glidingthroughspace/paper-tracker/paper/template/00_Latex/kopfundFusszeile.tex

%% spellcheck-off
% ---- Metainformation für das PDF Dokument
\hypersetup{
	pdftitle    = {\thetitle},
	pdfsubject  = {\arbeit},
	pdfauthor   = {\theauthor},
	%pdfkeywords = {Keywords angeben},
	pdfcreator  = {LaTeX},
	%pdfproducer = {in der Regel pdfTeX}
}

% ---- Definition der Kopf- und Fußzeilen
\clearscrheadfoot                               % Löschen von LaTeX Standard
\automark[section]{chapter}                     % Füllen von section und chapter
%\renewcommand*{\chaptermarkformat}{}            % Entfernt die Kapitelnummer
%\renewcommand*{\sectionmarkformat}{}            % Entfernt die Sectionnummer
% Angaben [für "plain"]{für "scrheadings"}
\ihead[]{}                                      % Kopfzeile links
\chead[]{}                                      % Kopfzeile mitte
\ohead[]{\rightmark}                            % Kopfzeile rechts
\ifoot[]{}                                      % Fußzeile links
\cfoot[]{}                                      % Fußzeile mitte
\ofoot[]{\sffamily\pagemark}                    % Fußzeile rechts
\KOMAoptions{headsepline = 0.1pt, footsepline = 0.1pt}
