glidingthroughspace/paper-tracker/paper/template/01_Standard/sperrvermerk.tex

\chapter*{Sperrvermerk}
Die nachfolgende Arbeit enthält vertrauliche Daten der:
\begin{quote}
	\firmaName \\
	\firmaStrasse \\
	\firmaPlz
\end{quote}

\vspace{0.5cm}

Sie darf als Leistungsnachweis des Studienganges \studiengang{} \studienjahr{} an der DHBW Karlsruhe verwendet und nur zu Prüfungszwecken zugänglich gemacht werden. Über den Inhalt ist Stillschweigen zu bewahren. Veröffentlichungen oder Vervielfältigungen der \arbeit{} - auch auszugsweise - sind ohne ausdrückliche Genehmigung der SAP SE nicht gestattet.

\vspace{0.5cm}

SAP und die SAP Logos sind eingetragene Warenzeichen der SAP SE. Die Wiedergabe von Gebrauchsnamen, Handelsnamen, Warenbezeichnungen usw. in dieser Arbeit berechtigt auch ohne besondere Kennzeichnung nicht zu der Annahme, dass solche Namen im Sinne der Warenzeichen-und Markenschutz-Gesetzgebung als frei zu betrachten wären und daher von jedem benutzt werden dürfen.
