glidingthroughspace/paper-tracker/paper/Studienarbeit.pdf

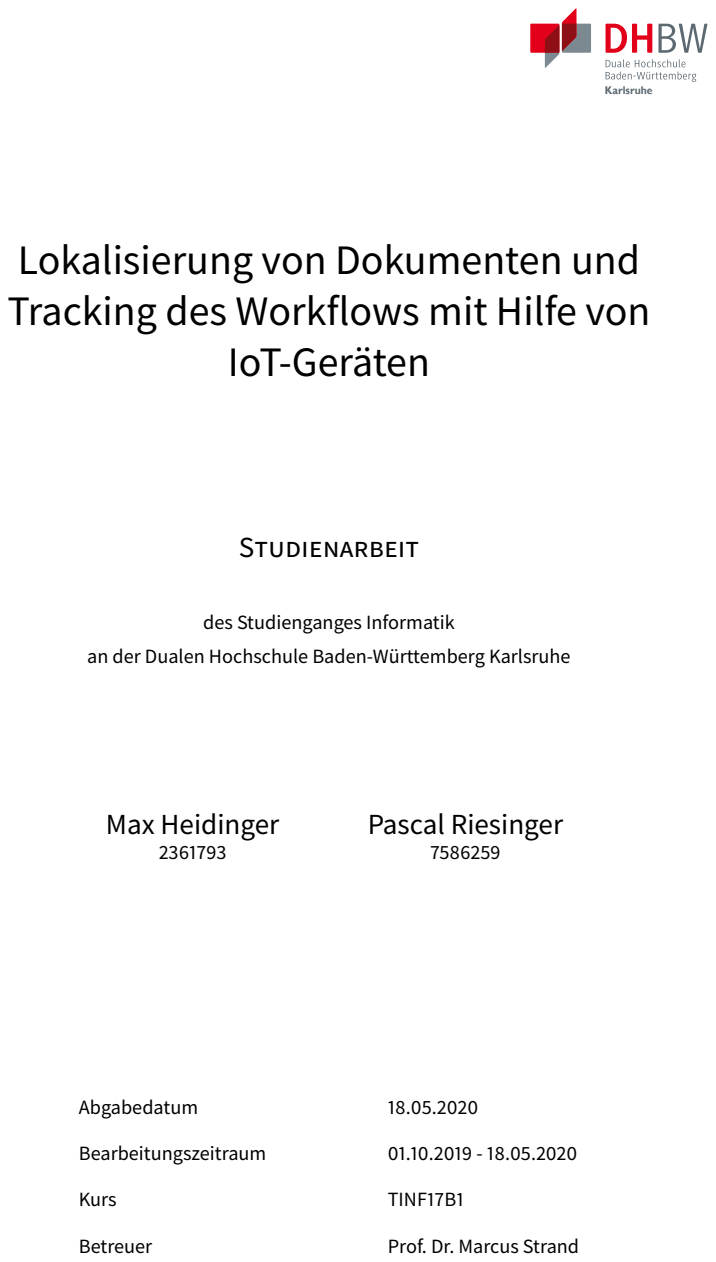
[picture p30: page 1]
Karlsruhe; IoT-Geräten; STUDIENARBEIT; Max Heidinger; Pascal Riesinger; Abgabedatum; Bearbeitungszeitraum; Kurs; TINF17B1; Betreuer; Prof. Dr. Marcus Strand

Lokalisierung von Dokumenten und

Tracking des Workflows mit Hilfe von

des Studienganges Informatik

an der Dualen Hochschule Baden-Württemberg Karlsruhe

# Eidesstattliche Erklärung

Wir versichern hiermit, dass wir unsere Studienarbeit mit dem Thema:

Lokalisierung von Dokumenten und Tracking des Workflowsmit Hilfe von IoT-Geräten

gemäß § 5 der „Studien- und Prüfungsordnung DHBW Technik“ vom 29. September 2017

selbstständig verfasst und keine anderen als die angegebenen Quellen und Hilfsmittel be-

nutzt habe. Die Arbeit wurde bisher keiner anderen Prüfungsbehörde vorgelegt und auch

nicht veröentlicht.

Wir versichern zudem, dass die eingereichte elektronische Fassung mit der gedruckten Fas-

sung übereinstimmt.

Karlsruhe, den 2. April 2020

Max Heidinger, Pascal Riesinger

# Inhaltsverzeichnis

Abkürzungsverzeichnis | IV
Abbildungsverzeichnis | VI
Listings | VII
1 | Einführung | 1
2 Grundlagen | 2
3 Analyse | 6
4 Entwurf | 8
5 Implementierung | 20

6 Validierung | 24
7 Ausblick und Weiterentwicklungen | 25
8 Zusammenfassung | 26
Glossar | 27
Literatur | VIII

# Abkürzungsverzeichnis

Akku Akkumulator. 22

AMQP Advanced Message Queuing Protocol. 14

AP Access Point. 2, 10

API Application Programming Interface. 22

BDD Behavior-driven development. 21

BSS Basic Service Set. II, 2, 3

BSSID Basic Service Set Identifiers. 2, 3, 12

CBOR Concise Binary Object Representation. 14, 21

CoAP Constrained Application Protocoll. 14, 18, 20

DHBW Duale Hochschule Baden-Württemberg. VI, 1–4

ESS Extended Service Set. II, 3

HTTP Hypertext Transfer Protocol. 14, 15, 18, 20

IEEE Institute of Electrical and Electronics Engineers. 2

IoT Internet of Things. 14

JSON JavaScript Object Notation. 14, 15, 20

LAN Local Area Network. 3

LED Light Emitting Diode. 22

MAC Media Access Control. 2

MQTT Message Queuing Telemetry Transport. 14

ORM Object-relational mapping. 20

REST Representational State Transfer. 15

RPCI Received Channel Power Indicator. 3

RSSI Received Signal Strength Indication. II, 3

SSID Service Set Identifier. 2, 3

UART Universal Asynchronous Receiver Transmitter. 22

USB Universal Serial Bus. 22

WLAN Wireless Local Area Network. II, 2, 10, 22

# Abbildungsverzeichnis

2.1 | Beschaungs-Genehmigungsverfahren der Duale Hochschule Baden-Württemberg
| (DHBW) | | 4
4.1 | Architektur des Paper-Tracker | | 9
4.2 | UML-Diagramm für die Backend-Anwendung | | 13
4.3 | Soware-Architektur für die Backend-Anwendung | | 19

# Listings

1 Einführung

# 1 Einführung

An der DHBW in Karlsruhe basieren, wie auch noch in vielen anderen Organisationen, viele Prozesse auf Papier. Dies bedeutet, dass beispielsweise für die Genehmigung eines Einkaufes, ein oder mehrere Blätter Papier von unterschiedlichen Personen unterzeichnet werden müssen. Dafür wird das Dokument durch die einzelnen Büros getragen, bis letztendlich der Antragssteller es wieder bekommt.

Auch für simple Prozesse kann dies einige Zeit in Anspruch nehmen. Während dieser ganzen Zeit hat der Antragsteller leider keine Einsicht, bei welcher Person sich die Papiere befinden. Damit kann er auch nicht versuchen den Prozess zu beschleunigen, ohne Schritt für Schritt bei allen Personen des Prozesses nachzufragen. Zusätzlich kann nach Abschluss des Prozesses nicht nachvollzogen werden, wo der Flaschenhals des Prozesses liegt.

Um dieses Problem anzugehen, wird der „Paper-Tracker“ entwickelt. Dieser soll eine Transparenz in alle auf Papier basierten Prozesse bringen und zusätzlich Daten liefern, um die Prozesse selbst zu optimieren.

## 1.1 Idee des Paper-Tracker

Der Paper-Tracker ist ein kleines Gerät basierend auf einem Mikrocontroller, welcher an den Dokumenten befestigt wird. Dieser soll eine Lokalisierung der Papiere ermöglichen. Auf diese Lokalisierung soll der Antragsteller eines Prozesses über eine App Zugriff bekommen. Weiter soll auch in der App für Mobilgeräte der komplette Prozess oder Workflow selbst verfolgt werden. Somit kann zum Beispiel auch eine Notifizierung zuständiger Personen für einen Schritt in einem Workflow erfolgen.

1

2 Grundlagen

# 2 Grundlagen

## 2.1 Projektumfeld

Das Projekt wird im Umfeld der DHBW Karlsruhe durchgeführt.

## 2.2 Funktionsweise WLAN

Unter WLAN versteht man im Allgemeinen ein Funknetz nach einem Standard der Institute of Electrical and Electronics Engineers (IEEE) 802.11 Familie. Alle Standards der
Familie basieren auf dem ursprünglichen 802.11 Standard und erweitern diesen um neue
Funktionalität, Frequenzen und höheren Datenraten. (vgl. [1]) | Primärquelle finden

Für die Funktionsweise des Paper-Trackers muss der Teil der „Service Sets“ der Spezifikation detailiert erleutert werden. Unter einem Service Set versteht man im Allgemeinen alle
Geräte in einem WLAN-Netzwerk. Auf diesen basiert die Lokalisierung der Dokumente.

### 2.2.1 BSS

Ein BSS ist Service Set, in dem es nur einen Access Point (AP) und damit ein Gerät, dass das Funknetz aufbaut, gibt. Zu diesem AP können beliebig viele Klienten verbunden sein. In einem solchen Netzwerk besitzt der AP eine Service Set Identifier (SSID) und eine Basic Service Set Identifiers (BSSID). Die SSID ist der Name des Netzwerks, das von einem Endbenutzer ausgewählt wird, um sich mit dem WLAN zu verbinden. Da mehrere
BSS die gleiche SSID verwenden können, besitzt der AP auch eine BSSID. Diese ist meist
die Media Access Control (MAC)-Adresse des AP, welche per Definition einzigartig ist.
(vgl. [2]) Mit Hilfe dieser BSSID können Klienten zwischen den verschiedenen Netzwerken Primärquelle finden (IEEE RFC) mit identischer SSID unterscheiden.

2

2 Grundlagen

### 2.2.2 ESS

In einem ESS existieren mehrere BSS, die miteinander z.B. über ein Local Area Network
(LAN) verbunden sind. Alle BSS in diesem Service Set haben eine eigene BSSID aber
bauen ein Netz mit der gleichen SSID auf. So können Klienten z.B. in größeren Gebäuden
zwischen verschiedenen BSS wechseln, ohne es zu bemerken. (vgl. [3]) | Primärquelle finden

### 2.2.3 Signalstärke RSSI

Die RSSI ist eine Größe, welche im Allgemeinen die Energie eines Radiosignals repräsentiert. Es gibt keine Standardisierung hinsichtlich der Messmethode oder der entstehenden Einheit, in welcher die RSSI angegeben wird. Da sie ein Maß für Dämpfung ist, wird jedoch immer eine negative Zahl angegeben. Je näher sich diese Zahl null nähert, desto stärker ist das Signal. Typischerweise liegt der Messwert im Bereich zwischen null und −100.

Als standardisierter Ersatz für die RSSI wurde der Received Channel Power Indicator (RPCI) eingeführt. Diese Größe wird immer in der Einheit dBm angegeben und wird über ein definiertes Intervall gemessen. Der Wertebereich bewegt sich dabei zwischen −110dBm und 0dBm. Repräsentiert wird die Messung als 8-Bit-Ganzzahl, was abzüglich einiger reservierter Werte zu einer maximalen Auflösung von 0.5dBm führt. Auch standardisiert ist die zu erreichende Genauigkeit, so soll die Abweichung bei maximial 5dBm liegen. (vgl. [4])

## 2.3 Beispiel eines Workflows

In folgender Abbildung 2.1 ist ein Beispiel für einen Prozess an der DHBW Karlsruhe dargestellt. Es ist das „Beschaffungs-Genehmigungsverfahren“, das benötigt wird, um eine Bestellung für die DHBW durchzuführen.

Der Prozess beginnt mit dem Antragsteller, welcher den Beschaffungsantrag stellt. Der Antrag geht zum Fachvorgesetzten des Antragsteller, welcher diesen fachlich prüft. Ist die Prüfung nicht erfolgreich, wird eine Ablehnung begründet und der Prozess beendet.

Bei erfolgreicher Prüfung muss der Antrag, wenn er über 5.000€ liegt, zudem vom Dekan

3

2 Grundlagen


Abbildung 2.1: Beschaffungs-Genehmigungsverfahren der DHBW

4

2 Grundlagen

geprüft werden. Dieser kann entweder den Antrag wie oben beschrieben ablehnen oder stimmt diesem zu.

Ist der Antrag für eine Bestellung unter 5.000€ oder er bekommt die Zustimmung des Dekans, erhält als nächstes die Verwaltung den Antrag. Die Verwaltung muss prüfen, ob die Mittel für diese Bestellung vorhanden sind. Sind die Mittel nicht vorhanden, wird der Antrag abgelehnt. Bei vorhandenen Mitteln wird der Antag von dem Verwaltungsdirektor unterschrieben und damit freigegeben. Damit wird die Beschaffung in der Verwaltung vorgemerkt und der Antrag geht an den ursprünglichen Antragsteller zurück.

Sobald der Antragsteller den unterzeichneten Antrag erhält, kann die Beschaffung erfolgen. In diesem Schritt müssen mögliche nicht berücksichtigte Bieter im Falle einer Ausschreibung informiert werden.

Im letzten Schritt veröffentlicht die Verwaltung das Ergebnis der Beschaffung auf der Homepage und der Prozess ist erfolgreich abgeschlossen.

5

3 Analyse

# 3 Analyse

In den folgenden Abschnitten werden der Ist-Zustand, aus welchem sich die Problemstellung ergibt, der Soll-Zustand, sowie die gestellten Anforderungen beschrieben.

## 3.1 Ist-Analyse

Es besteht das Problem, dass der aktuelle Status eines auf Papier basierten Prozesses nicht nachvollzogen werden kann. Für den Antragsteller eines Prozesses ist es nicht möglich herauszufinden, bei welcher Person oder in welchem Raum sich ein Dokument zu einem bestimmten Zeitpunkt befindet. Zusätzlich kann, sobald der Prozess beendet ist, nicht herausgefunden werden, an welcher Stelle im Prozess zum Beispiel eine besonders hohe Wartezeit stattgefunden hat.

## 3.2 Soll-Analyse

Ziel der Entwicklung und damit dieser Studienarbeit ist das Erarbeiten einer Lösung, mit welcher die aktuelle Position eines Dokuments und der aktuelle Fortschritt des Prozesses sichtbar gemacht werden kann. Es soll ein möglichst unauffälliges Gerät sein und eine intuitive Bedienung ermöglichen. Über aktuelle und abgeschlossene Prozesse sollen Da-

ten analysiert werden können, um Möglichkeiten zur Prozessoptimierungen erkennen zu können.

## 3.3 Anforderungsanalyse

Im Folgenden werden die gestellten Anforderungen in funktionale und nichtfunktionale Anforderungen unterteilt. Dabei beschreiben funktionale Anforderungen konkrete Funk- Evtl. noch eine Anfor- derungs- analyse mit ande- ren Leuten durchführen tionen, die die entwickelte Lösung bieten muss, nichtfunktionale Anforderungen hingegegen zeigen Rahmenbedingungen, sowie Anforderungen an die technische Umsetzung auf.

6

3 Analyse

Desweiteren werden den Anforderungen Prioritäten zugewiesen, wobei ein Wert von 0 die höchste Priorität, ein Wert von 3 die niedrigste Priorität beschreibt, sodass die Lösung ohne Erfüllung der Anforderungen mit Priorität 0 nicht einsetzbar ist und Priorität 3 optionale Funktionalitäten beschreibt, die nicht zum Betrieb notwendig sind.

F-1 P0 Der Standort von Dokumenten kann raumgenau verfolgt werden

F-2 P0 Der aktuelle Status des mit dem Dokument verbundenen Workflows kann nachvollzogen werden

F-3 P2 Neue Workflows können vom Nutzer definiert werden

F-4 P1 Neue Tracker können dem System vom Nutzer hinzugefügt werden

F-5 P2 Der Raumplan kann vom Nutzer eingelernt werden

F-6 P3 Nutzer werden vom System benachrichtigt, wenn die Akkuladung eines Trackers unter einen gegebenen Prozentsatz fällt oder die Batterie ausgetauscht werden muss

F-7 P1 Einzelne Schritte von Workflows können optional sein und übersprungen werden

F-8 P1 Für einen Schritt im Workflow können mehrere Orte hinterlegt werden

NF-1 P2 Die Laufzeit der Tracker im Batteriebetrieb beläuft sich auf mindestens eine Woche

NF-2 P1 Die Tracker sollen möglichst unscheinbar und daher klein und leicht sein

NF-3 P0 Die Daten können in einer Applikation für Mobiltelefone abgefragt werden. Dabei ist besonders die Verwendbarkeit unter dem Betriebssystem Android wichtig, die Unterstützung von iOS ist optional

NF-4 P1 Die Anwendung muss stabil laufen und sollte sich nicht unerwartet beenden

NF-5 P2 Die Lösung sollte skalierbar hinsichtlich der Anzahl der Tracker und der Größe des Tracking-Bereiches sein

NF-6 P2 Zur optimalen Nachvollziehbarkeit von Workflows sollten deren auch nach Abschluss nicht gelöscht werden

NF-7 P2 Die im System gespeicherten Daten sollen in einem maschinenlesbaren Format exportiert werden können, um Auswertungen über die Effizienz der Workflows durchführen zu können

7

4 Entwurf

# 4 Entwurf

## 4.1 Systemarchitektur

In Abbildung 4.1 ist eine grobe Übersicht über die verschiedenen Komponenten des Pro-

jektes gegeben. Es besteht aus drei Komponenten:

- Hardware-Tracker
- Backend-Anwendung
- App

Der Hardware-Tracker ist die physische Komponente, die direkt an ein zu trackendes Papier angeheftet wird. Er wird regelmäßig Daten erfassen und diese zur Lokalisierung an die Backend-Anwendung senden.

Die Backend-Anwendung dient als zentrales Element der Architektur. Sie bekommt Daten des Trackers zugeschickt, wertet diese aus und speichert sie. Auch das Management der Räume und Workflows wird von der Anwendung übernommen.

Nutzer verwenden zur Kommunikation mit dem Backend eine Smartphone-App. Sie kommuniziert ebenfalls mit der Backend-Anwendung und fragt von dieser Informationen an oder löst Aktionen aus.

Die Entwürfe der drei Komponenten werden in den nachfolgenden Abschnitten im Detail erläutert.

8

4 Entwurf

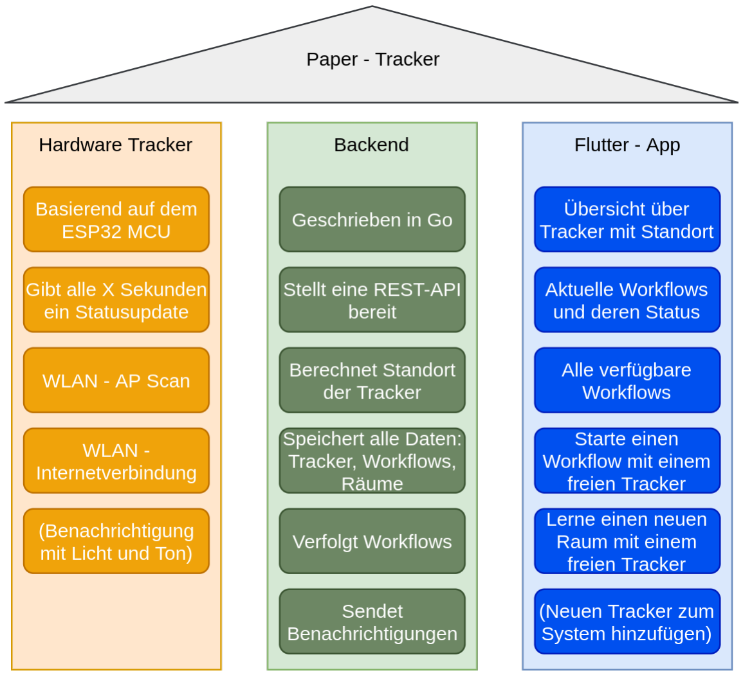
[picture p31: figure]

Abbildung 4.1: Architektur des Paper-Tracker

9

4 Entwurf

## 4.2 Komponentenarchitektur

In den folgenden Abschnitten wird detaillierter auf die einzelnen Komponenten des in Abschnitt 4.1 beschriebenen Systems eingegangen. Dabei werden die Komponenten in derselben Reihenfolge beschrieben, in welcher die Daten im Gesamtsystem fließen.

### 4.2.1 Tracking mit IoT-Hardware

Zur Erfassung der Standortdaten der Dokumente werden, wie in Abschnitt 3.2 beschrieben, Hardware-Tracker eingesetzt. Diese verwenden jedoch keine absolute Positionierungs- Es wä- re schön, Glossar- Referenzen zu kenn- zeichnen (oft mit Glos, oder Gls)technologie wie beispielsweise GPS, da das hierfür benötigte Satellitensignal in Gebäuden
zu schwach, und somit die Positionierung fehlschlagen kann.

Quelle für
die Genauigkeit von
GPS in Gebäuden

Ist das hier
eher Analyse?

Für die Lokalisierung von Geräten innerhalb eines Gebäudes gibt es daher mehrere Ansätze. Eine Möglichkeit ist es, ein Mesh-Netzwerk aus den Tracker-Geräten aufzubauen.

Glossar:
Mesh-Netzwerk

Ist die Position einiger weniger Knoten des Meshes bekannt, kann durch die Signalstärke zu umliegenden Knoten oder über die sogenannte Time-of-Arrival bestimmt werden, wo sich ein Knoten relativ zu anderen Knoten und damit auch zu den Knoten mit bekannter Position befindet. Mit dieser Methode kann eine Genauigkeit von bis zu einem Meter bei

Time-of-Arrival erläutern

der Lokalisierung erzielt werden. (vgl. [5])

Eine weitere Möglichkeit ist, auf bestehende Infrastruktur zurückzugreifen. WLAN ist heutzutage in praktisch jedem Gebäude verfügbar. In Gebäuden, in welchen es mehrere APs gibt, kann die Position dadurch bestimmt werden, dass der Tracker auswertet, von welchen APs er ein Signal empfängt und wie stark der Empfang zum jeweiligen AP
ist. Da die Positionsdaten ohnehin zur Auswertung an das Backend übertragen werden
müssen, wofür eine WLAN-Verbindung notwendig ist, wird diese Methode eingesetzt. Die
gesammelten Daten werden dann im Anschluss an das Backend übermittelt. | Lifecycle des Paper- Trackers erläutern

10

4 Entwurf

### 4.2.2 Backend-Anwendung

UML Daten Modellierung

Da die Backend-Anwendung die zentrale Komponente des Systems ist und auch die Daten verwaltet, werden für sie die Daten-Klassen modelliert. Das resultierende UML-Diagramm ist in Abbildung 4.2 abgebildet.

Die zentrale Klasse des Diagramms bildet die „Tracker“-Klasse. Sie modelliert einen Hardware-Tracker. Neben einigen Attributen, wie dem Label, der Batteriestatus und einigen gespeicherten Zeitstempeln, besitzt sie eine Referenz auf einen Status. Dieser Status gibt an, zu was der Tracker zur Zeit verwendet wird und in welchen anderen Zustand gewechselt werden kann.

Es gibt vier verschiedene Zustände, die in Integern kodiert sind:

Idle = 1
Tracker ist frei verfügbar und kann in „Learning“ oder „Tracking“ übergehen.

Learning = 2
Tracker wird für das Lernen eines Raumes verwendet und kann bei erfolgreichem Abschluss in „LearningFinished“ oder bei Abbruch in „Idle“ übergehen.

LearningFinished = 3
Das Lernen eines Raumes mit diesem Tracker wurde beendet. Die Ergebnisse können berechnet und einem Raum zugewiesen werden. In Folge darauf, geht der Tracker in den Zustand „Idle“ über.

Tracking = 4
Der Tracker besitzt aktuell einen Workflow, den er trackt. Nach Abschluss dieses Workflows oder nach Abbruch, geht der Tracker in den Status „Idle“ über.

Weiter besitzt der Tracker eine Referenz auf einen aktiven Workflow und den aktuellen Raum. Beide Referenzen können nichtexistent sein, falls der Tracker keinen aktiven Workflow besitzt oder der Raum nicht bestimmbar ist.

Ein „Room“ ist ein physikalischer Raum, der von einem Tracker erkannt werden soll. Neben einem Identifizierer und einem „Label“ (Name) für den Raum werden zusätzlich mehrere „BSSIDTrackingData“ gespeichert. Diese beinhalten für einen spezifischen „Access

11

4 Entwurf

Point“/BSSID einige Messdaten zu der gemessenen Signalstärke. Über diese kann über eine

Antwort des Trackers mit „ScanResults“ die Position des Tracker bestimmt werden.

Damit der Tracker eine Antwort sendet, wird diese mit Hilfe eines Kommandos angefragt. Diese Kommandos werden jeweils in einer Instanz der „Command“-Klasse abgebildet. Die Kommandos besitzen einen spezifischen Typ der Enumeration „CommandType“, der die Aktion des Kommandos bestimmt. Auch wird pro Kommando eine „SleepTimeSec“ festgelegt, die bestimmt wie lange der Tracker sich nach der Aktion abschalten darf.

Spezielle Antworten der Tracker auf Kommandos und auch des Servers auf Anfragen der App sind in dem Unterpaket „communication“ modelliert. Dies ist zum Beispiel eine Fehler-Antwort und eine Basisklasse für Antworten des Trackers. Diese „TrackerResponse“-Klasse besitzt auch ein Feld für den aktuellen Batteriestand des Trackers, um diesen überwachen zu können.

Unter den Klassen „WorkflowTemplate“ und „WorkflowExec“ sind die Workflows modelliert. „WorkflowTemplate“ stellt eine Blaupause dar, wie ein Workflow aussieht. In diesem werden die einzelnen Schritte („Steps“) des Workflows festgelegt. Für einen „Step“ werden ein Label und eine Referenz auf den dazugehörigen Raum gespeichert. Über die Klasse

„NextStep“ werden Referenzen auf nachfolgende Schritte modelliert. Die „NextStep“ Klasse besitzt ein Attribut „DecisionLabel“. Ist diese ein leerer String, so ist dieser verbundene Schritt ein linearer. Mit einem nicht-leeren String, gibt es mit diesem Schritt verschiedene Auswahlmöglichkeiten. Durch das transitive Attribut „StepEditingLocked“ der „Workflow-Template“-Klasse, wird die Bearbeitung blockiert. Dieses Attribut ist gesetzt, sobald es eine Ausführung des Templates gab.

Die „WorkflowExec“-Klasse stellt einen konkreten Workflow in der Durchführung dar. Als Attribute besitzt diese Klasse ein Label, einen Status und Start-/Endzeit. Der Status ist entweder „Running“, „Completed“ oder „Canceled“. Weiter besitzt die Klasse eine Referenz auf das Template, das ausgeführt wird, eine Menge an „ExecStepInfo“ und an den aktuellen Schritt. Die Klasse „ExecStepInfo“ besitzt Informationen über einzelne Schritte des Workflows. Dies sind zum einen die Start-/Endzeit des Schrittes sowie, ob der Schritt übersprungen wurde, und zum anderen die „Decision“-Information. Der „Decision“ String wird im Falle von mehreren Auswahlmöglichkeiten in einem Workflow dazu genutzt, in der Ausführung den richtigen Weg zu wählen.

12

4 Entwurf

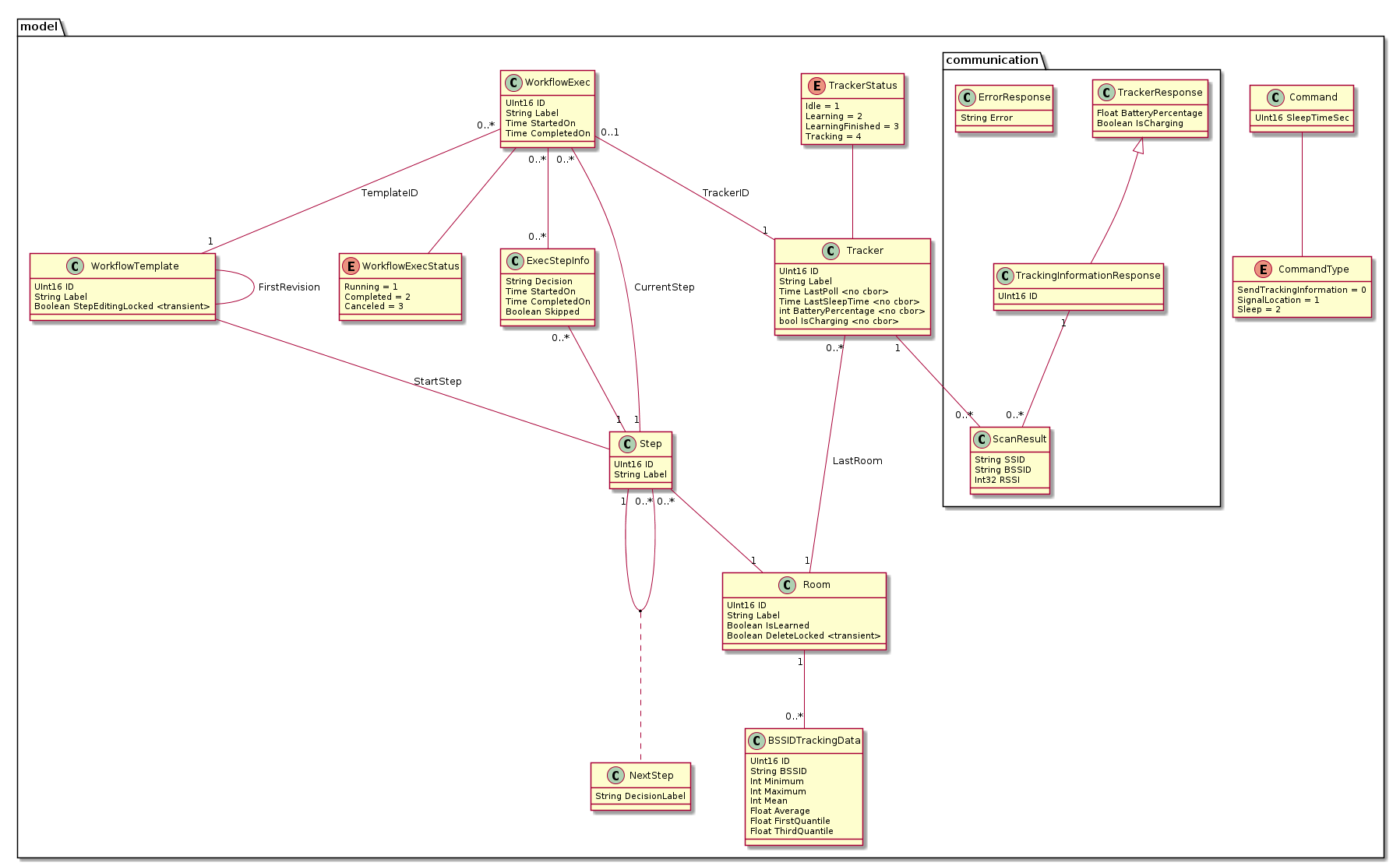
[picture p32: figure]

Abbildung 4.2: UML-Diagramm für die Backend-Anwendung

13

4 Entwurf

Schnittstellen

Für die Backend-Anwendung sind zwei verschiedene Schnittstellen vorgesehen. Eine Schnittstelle ist für den Tracker und eine für die App vorgesehen. Die unterschiedlichen Schnittstellen sollen die aus der Analyse entwickelten Ansprüche entsprechend erfüllen.

Tracker-Schnittstelle Für die Schnittstelle des Trackers bedeutet dies, dass sie möglichst simpel und effizient sein muss. Dies wird über ein entsprechendes Protokoll und einem Datenformat erreicht. Das verwendete Protokoll ist das Constrained Application Protocoll (CoAP) Protokoll und das Datenformat ist Concise Binary Object Representation (CBOR).

Bei Constrained Application Protocoll (CoAP) handelt es sich um ein spezialisiertes Protokoll für die Verwendung in Internet of Things (IoT)-Hardware, welches dafür optimiert wurde möglichst wenig Overhead zu haben.

Im IoT-Bereich haben sich einige Protokolle durchsetzen können. Dazu zählen vor allem Hypertext Transfer Protocol (HTTP), Message Queuing Telemetry Transport (MQTT), Advanced Message Queuing Protocol (AMQP) und CoAP. Da die Tracker batteriebetrieben sind, ist für diesen Anwendungsfall besonders die Performance des eingesetzten Protokolles wichtig. Je weniger Overhead das Protokoll aufweist, desto weniger Instruktionen müssen vom Prozessor des Trackers durchgeführt werden, was zu einer längeren
Laufzeit führt. Werden die Protokolle anhand dieses Aspektes verglichen, erweist sich
CoAP als effizientestes Protokoll. (vgl. [6], [7]) | Quellen ver- wenden, die in diesem Paper zi- tiert werden

Concise Binary Object Representation (CBOR) ist ein Datenformat, das auf kleine Codeund Nachrichtengrößen optimiert ist. Demnach ist es auch für der IoT-Bereich sehr gut geeignet. Vom Aufbau des Formats, ist es sehr gut mit JavaScript Object Notation (JSON) zu vergleichen, da es auch Schlüssel-Wert-Paare verwendet. Der große Unterschied ist jedoch, dass CBOR binär kodiert wird und JSON in Text kodiert wird. Dadurch ist CBOR nicht menschenlesbar aber sehr gut maschinenlesbar. Bei einem Vergleich zwischen der
CBOR Bibliothek „libCBOR“ und der JSON Bibliothek „ArduinoJson“ konnte zudem festgestellt werden, dass bei gleicher Nachricht das CBOR Format ca. 26.5% kleinere
Nachrichten in 83.3% der Zeit schnellerer Zeit serialisiert hat. | Hier das Polling- Prinzip oder unter Hard- ware?!

Die Tracker-Schnittstelle soll drei Endpunkte zur Verfügung stellen. Diese sind in Tabel-

14

4 Entwurf

Verb | Pfad | Aktion | Rückgabe-Wert
POST | /tracker/new | Neuen Tracker erstellen | Tracker ID
GET | /tracker/poll | Kommando für Tracker abfragen | Tracker Kommando
POST | /tracker/tracking | Ergebnisse des Tracking speichern | -

Tabelle 4.1: Verfügbare Endpunkte der Tracker-Schnittstelle

le 4.1 aufgelistet. Bis auf den Endpunkt zum erstellen eines neuen Trackers, erhalten alle Endpunkte als Parameter die Tracker ID des Trackers, der die Anfrage stellt. Der Endpunkt zum Speichern der Tracking Ergebnisse hat zudem als Parameter die Ergebnisste selbst.

App-Schnittstelle Die Schnittstelle für die App hat keine besonderen Anforderungen
und kann daher frei gewählt werden. Aus diesem Grund werden Protokolle und Datenformate verwendet, die momentan dem aktuellen Stand der Technik entsprechen. Dies Quelle für aktuelle Protokol- le ergibt den Vorteil, dass sie mit allen anderen gewählten Technologien sehr gut kombinierbar sind und entsprechende Bibliotheken vorhanden sind. Das verwendete Protokoll
ist das HTTP-Protokoll und das Datenformat ist JSON. Die Schnittstelle basiert auf
dem Representational State Transfer (REST) Paradigma. Alle verfügbaren Endpunkte | Soll REST
| erläutert
der App-Schnittstelle sind in Tabelle 4.2 dargestellt. | werden?

Zwischen"überschriften"hinzufügen für Room,
Tracker, etc.

Erläuterung
der einen
Abkürzung
(wf)?

Hinzufügen
einer caption führt zu
Fehlern

15

4 Entwurf

Verb Pfad Aktion Parameter Rückgabe-Wert
GET /room Auflistung der Räume - Liste aller Räume
POST /room Erstellen eines neuen Raums Raum Erstellter Raum

PUT /room/:id Raum aktualisieren Raum Aktualisierter Raum
DELETE /room/:id Raum löschen - - GET /tracker Auflistung der Tracker - List aller Tracker

PUT /tracker/:id Tracker aktualisieren Tracker Aktualisierter Tracker

DELETE /tracker/:id Tracker löschen - - POST /tracker/:id/learn Lernen mit Tracker starten - Lernzeit

# GET /tracker/:id/learn Lern Status abfragen - Abgeschlossen

Gefundene SSIDs
DELETE /tracker/:id/learn Lernen abbrechen - - POST /tracker/:id/learn/finish Lernen abschließen Raum ID

SSIDs

GET /workflow/template Auflistung der Templates - Liste aller Templates
POST /workflow/template Template erstellen Template Erstelltes Template

PUT /workflow/template/:id Template aktualisieren Tempalte Aktualisiertes Template

16

4 Entwurf

Verb Pfad Aktion Parameter Rückgabe-Wert
DELETE /workflow/template/:id Template löschen - - POST /workflow/template/:id/start Start Schritt erstellen Step Erstellter Step

POST /workflow/template/:id/step Schritt hinzufügen

Step

Vorgänger ID

Erstellter Step

GET /workflow/template/:id/step/:id Schritt abfragen - Step

PUT /workflow/template/:id/step/:id Schritt aktualisieren Step Aktualisierter Step
DELETE /workflow/template/:id/step/:id Schritt löschen - - POST /wf/template/:id/step/:id/move Schritt verschieben Richtung - POST /workflow/template/revision Template Revision erstellen Label Erstellte Revision

GET /workflow/exec Auflistung der Ausführungen - Execution

POST /workflow/exec Ausführung erstellen Execution Erstelle Execution

POST /workflow/exec/:id/progress/:id Ausführung zu Schritt progressieren - - POST /workflow/exec/:id/cancel Ausführung abbrechen - -

17

4 Entwurf

Soware-Architektur

Die Architektur des Backend-Servers ist in folgendem Klassendiagramm 4.3 dargestellt. Layout ver- bessern, Er- stellung der DB Verbin- dung rein- packen

Generell kann die Architektur in drei verschiedene Schichten aufgeteilt werden. Die erste
Schicht bildet das Paket „router“, die zweite Schicht das Paket „managers“ und die dritte
Schicht das Paket „repositories“.

Im „router“ Paket befinden sich die Router für die zwei externen Schnittstellen des Servers. Die HTTP Schnittstelle für die App befindet sich in der „HttpRouter“-Klasse und die CoAP Schnittstelle für den Tracker befindet sich in der „CoapRouter“-Klasse. Beide Klassen besitzen eine Methode „Serve“. Mit dieser Methode werden die Router letztendlich gestartet so, dass sie Verbingungen annehmen können. Als Parameter bekommen sie die Adresse, auf die sie Verbindungen annehmen, und im Falle des „CoapRouter“ auch das Transport-Protokoll.

Das „managers“ Paket beinhaltet sechs verschiedene Manager, die die Businesslogik für verschiedene Teilbereiche des Servers beinhalten. Ein Beispiel ist der „TrackerManager“, über den Tracker angelegt, abgefragt, verändert und auch gelöscht werden können. Weitere Methoden für z.B. das Abfragen eines Kommandos für einen Tracker sind auch beinhaltet. Alle Manager sind als Singleton implementiert so, dass sie sich auch untereinander problemlos aufrufen können.

Die unterste Schicht bildet das „repositories“ Paket. Dieses enthält verschiedene Datenbank-Repositories, die die Datenbank und damit die Datenpersistenz des Servers abbilden. Alle Methoden eines Repository bilden direkte Anfragen an die Datenbank. Dabei ist ein Repository meist für eine Modellklasse verantwortlich.

Die main-Klasse ist für das Starten des Servers und das Erstellen der einzelnen Komponenten verantwortlich.

18

4 Entwurf

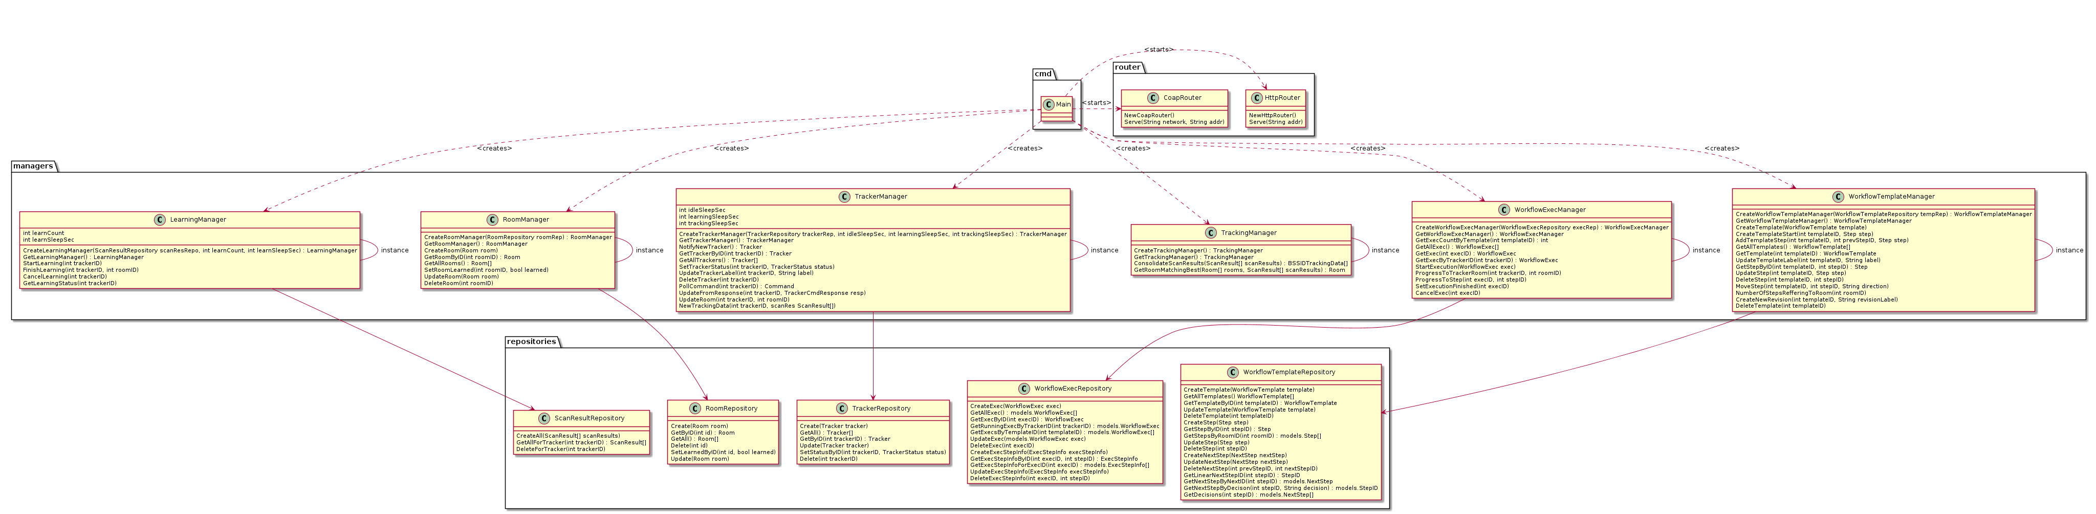
[picture p33: figure]

Abbildung 4.3: Software-Architektur für die Backend-Anwendung

### 4.2.3 App für Mobilgeräte

19

5 Implementierung

# 5 Implementierung

## 5.1 Backend-Server

### 5.1.1 Verwendete Technologien

Die grundlegend verwendete Technologie für den Backend-Server ist die Programmiersprache „Go“. Go wurde ausgewählt, da es eine einfach zu verstehende Programmiersprache ist, die optimiert für Server-Anwendungen ist (vgl. [8]). Zudem sind alle am Projekt beteiligten Personen schon mit der Sprache vertraut.

Go stellt eine gute Standardbibliothek zur Verfügung, die an vielen Stellen verwendet wird. Trotzdem werden zusätzlich einige externe Bibliotheken verwendet. Diese dienen hauptsächlich dazu, die externen Schnittstellen (HTTP und CoAP) mit den dazugehörigen Datenformaten zur Verfügung zu stellen. Auch werden Bibliotheken für ein einfacheres Testing verwendet.

Im Folgenden sind die verwendeten Bibliotheken aufgelistet:

logrus (https://github.com/sirupsen/logrus)
„logrus“ ist strukturiertes Logging-Tool, dass für jegliche Logs innerhalb des Servers verwendet wird.

gorm (https://github.com/jinzhu/gorm)
„gorm“ ist ein Object-relational mapping (ORM) Framework, dass die Datenbankanbindung für den Server zur Verfügung stellt.

Gin (https://github.com/gin-gonic/gin)
„Gin“ ist ein HTTP Framework, dass Routing, Parameter-Matching, etc. übernimmt. Zudem kann es standardmäßig JSON verstehen.

go-coap (https://github.com/go-ocf/go-coap)
„go-coap“ ist ein CoAP Framework, dass hauptsächlich das Routing übernimmt. Einige weitere Aufgaben, die z.B. „Gin“ übernimmt, müssen selbst programmiert

20

5 Implementierung

werden.

go-codec (https://github.com/ugorji/go)
„go-codec“ stellt die Codierung für CBOR zur Verfügung.

ginkgo (https://github.com/onsi/ginkgo)
Mit „ginkgo“ können Tests in Behavior-driven development (BDD) Technik geschrieben werden.

gomega (https://github.com/onsi/gomega)
„gomega“ ist eine Matching Library, die zu „ginkgo“ gehört. Sie stellt Vergleiche zwischen erwarteten Werten und tatsächlichen Werten zur Verfügung.

GoMock (https://github.com/golang/mock)
„GoMock“ ist ein Mocking Framework, dass für verschiedene Tests verwendet wird.

Als Datenbank wird in Kombination mit „gorm“ eine „SQLite“ verwendet. Der große Vorteil ist, dass eine SQLite Datenbank eine einfache Datei ist und kein externer Server aufgesetzt werden muss. Dies vereinfacht vor allem die Entwicklung. Zum Beispiel ist ein einfaches Zurücksetzten der Daten durch ein Löschen der Datei möglich.

In einem späteren Einsatz des Paper-Trackers kann dank der „gorm“ Bibliothek auch andere Datenbanken verwendet werden, die eher für einen dauerhaften und sichereren Einsatz vorgesehen sind. Möglich sind dafür „MySQL“, „PostgreSQL“, „Microsoft SQL Server“ und wie erwähnt SQLite. Im Code des Servers muss hierfür lediglich eine erweiterte Konfiguration ermöglicht werden. (vgl. [9])

21

5 Implementierung

### 5.1.2 Architektur

### 5.1.3 Analyse-Algorithmus

### 5.1.4 REST-Schnittstelle

### 5.1.5 COAP-Schnittstelle

## 5.2 Hardware und Firmware

Im Folgenden wird erläutert, wie der Tracker hinsichtlich der verwendeten Hardware und der entsprechenden Firmware implementiert wurde.

### 5.2.1 Verwendete Technologien

Als Mikrokontrollerplattform wurde die sogenannte „TinyPICO“-Plattform gewählt. Nach eigener Aussage handelt es sich dabei um die kleinste vorgefertigte Entwicklungsplattform basierend auf Mikrocontrollern vom Typ ESP32. Dieser Aspekt ist für die Erfüllung von NF-2 wichtig. Dieser Mikrocontroller wurde gewählt, da er alle benötigten Funktionen wie beispielsweise WLAN bereits über ein Application Programming Interface (API) bereitstellt.

Die TinyPICO-Entwicklungsplattform stellt neben dem Mikrocontroller weitere Hardware bereit, so sind unter anderem die Stromversorgung über Universal Serial Bus (USB) sowie Lithium-Polymer-Akkumulator (Akku), ein Übersetzer von USB zu Universal Asynchro-

nous Receiver Transmitter (UART) zur Programmierung des Mikrocontroller und eine Vollspektrum-Light Emitting Diode (LED) verbaut. Ein weiterer Vorteil ist das bereits integrierte Ladesystem, welches einen angeschlossen Lithium-Polymer-Akku automatisch auflädt, sobald der Tracker über USB mit einer Stromquelle verbunden wird. Außerdem können über das Ladesystem der aktuelle Ladezustand und die Spannung des Akku abgefragt werden, was für die Erfüllung von F-6 unabdingbar ist.

Die Firmware wurde in der Programmiersprache C++ auf Basis des Arduino-Frameworks erstellt. Dieses Framework wurde gewählt, da es auf vielen Plattformen, wie auch dem

22

5 Implementierung

ESP32 lauffähig ist, weit verbreitet ist und somit viele Bibliotheken für das Framework existieren.

## 5.3 App

Im diesem Kapitel wird die technische Umsetzung der App für Mobilgeräte beschrieben.

### 5.3.1 Verwendete Technologien

Zur Programmierung der App wurden die Programmiersprache Dart und das Framework Flutter verwendet. Ein großer Vorteil dieser Kombination ist, dass Anwendungen sowohl für Android, als auch für iOS kompiliert werden können, ohne den Quellcode anpassen zu müssen. Auch eine Laufzeitumgebung für Desktopcomputer unter Windows, macOS und GNU/Linux befindet sich aktuell im Teststadium, sodass die Paper-Tracker App gegebenenfalles auch auf Arbeitsplatzrechnern verwendet werden kann.

## 5.4 Bekannte Probleme

### 5.4.1 Ungenauigkeit des Tracking

### 5.4.2 UI-Details in der App

23

6 Validierung

# 6 Validierung

## 6.1 Genauigkeitsmessung des Tracking

### 6.1.1 Beschreibung

### 6.1.2 Durchführung

### 6.1.3 Ergebnisse

## 6.2 Nutzerumfrage zur UX der App

### 6.2.1 Beschreibung

### 6.2.2 Durchführung

### 6.2.3 Ergebnisse

### 6.2.4 Gesamtergebniss der Validierung

24

7 Ausblick und Weiterentwicklungen

# 7 Ausblick und Weiterentwicklungen

## 7.1 Audiovisuelle Signale

## 7.2 Verbessertes Gehäuse

## 7.3 Tracking von Smartphones

Es ist wünschenswert, dass eine Person, die einen Raum betritt, in welchem ein Dokument auf deren Bearbeitung wartet, darüber informiert wird. Zu diesem Zweck können Smartphones in das Tracking-System mit aufgenommen werden.

25

8 Zusammenfassung

# 8 Zusammenfassung

26

Glossar

# Glossar

GPS Das Global Positioning System (GPS) ist ein von den Vereinigten Staaten von Amerika entwickeltes globales Navigationssystem, welches im zivilen, kommerziellen, wissenschaftlichen und militärischen Bereich Anwendung findet, um die Position von GPS-Empfängern zu bestimmen. (vgl. [10]). 10

Overhead Also Overhead werden Metadaten bezeichnet, welche zusätzlich zu den eigentlichen Nutzdaten anfallen. Beispiele für Overhead sind Prüfsummen, Netzwerkadres-
sen, oder Codierungszeichen . 14 | Quelle für Overhead suchen

27

# Literatur

[1] Schnabel, P. IEEE 802.11 / WLAN-Grundlagen. 03/2020. url: https://www.elektronik-kompendium.de/sites/net/0610051.htm (besucht am 27. 03. 2020) (siehe
S. 2).
[2] Luber, S. Was ist eine MAC-Adresse? 08/2018. url: https://www.ip-insider.de/was-ist-eine-mac-adresse-a-665074/ (https://www.ip-insider.de/was-ist-eine-mac-adresse-a-665074/) (besucht am 27. 03. 2020) (siehe S. 2).
[3] Haider, Z. 802.11 Topologies AKA Service Sets. 03/2019. url: https://www. wifi- professionals.com/2019/03/802-11- topologies-aka- service- sets (https://www.wifi-professionals.com/2019/03/802-11-topologies-aka-service-sets) (besucht am
27. 03. 2020) (siehe S. 3).
[4] „IEEE Standard for Information technology–Telecommunications and information exchange between systems Local and metropolitan area networks–Specific requirements Part 11: Wireless LAN Medium Access Control (MAC) and Physical Layer (PHY) Specifications“. In: IEEE Std 802.11-2012 (Revision of IEEE Std 802.11-2007) (03/2012) (siehe S. 3).
[5] Patwari, N. u. a. „Relative location estimation in wireless sensor networks“. In: IEEE Transactions on Signal Processing 51.8 (08/2003), S. 2137–2148 (siehe S. 10).
[6] Dizdarević, J. u. a. „A Survey of Communication Protocols for Internet of Things and Related Challenges of Fog and Cloud Computing Integration“. In: ACM Computing Surveys 51.6 (01/2019), S. 1–29 (siehe S. 14).
[7] Naik, N. „Choice of effective messaging protocols for IoT systems: MQTT, CoAP, AMQP and HTTP“. In: 2017 IEEE International Systems Engineering Symposium (ISSE). IEEE, 10/2017 (siehe S. 14).
[8] Weigend, J. Microservices mit Go | Informatik Aktuell. 06/2019. url: https:
//www.informatik-aktuell.de/entwicklung/methoden/microservices-mit-go.html (besucht am 01. 04. 2020) (siehe S. 20).
[9] Jinzhu. Connecting to database | GORM. 03/2020. url: https://gorm.io/docs/
connecting_to_the_database.html (https://gorm.io/docs/connecting_to_the_database.html) (besucht am 01. 04. 2020) (siehe S. 21).

[10] Department Of Transportation, F. A. A. Global Positioning System Wide Area Augmentation System (WAAS) Performance Standard. 10/2008. url: https://web.archive.org/web/20170427033332/http://www.gps.gov/technical/ps/2008-WAAS-performance-standard.pdf (https://web.archive.org/web/20170427033332/http://www.gps.gov/technical/ps/2008-WAAS-performance-standard.pdf) (besucht am 30. 10. 2019) (siehe S. 27).

# Todo list

o | | | 2
o | Primärquelle finden | | 2
o | Primärquelle finden (IEEE RFC) | | 2
o | Primärquelle finden | | 3
o | Evtl. noch eine Anforderungsanalyse mit anderen Leuten durchführen | | 6
o | Es wäre schön, Glossar-Referenzen zu kennzeichnen (oft mit Glos, oder Gls) . . | 10
o | Quelle für die Genauigkeit von GPS in Gebäuden | | 10
o | Ist das hier eher Analyse? | | 10
o | Glossar: Mesh-Netzwerk | | 10
o | Time-of-Arrival erläutern | | 10
o | Lifecycle des Paper-Trackers erläutern | | 10
o | Quellen verwenden, die in diesem Paper zitiert werden | | 14
o | Hier das Polling-Prinzip oder unter Hardware?! | | 14
o | Quelle für aktuelle Protokolle | | 15
o | Soll REST erläutert werden? | | 15
o | Zwischen"überschriften"hinzufügen für Room, Tracker, etc | | 15
o | Erläuterung der einen Abkürzung (wf)? | | 15
o | Hinzufügen einer caption führt zu Fehlern | | 15
o | Layout verbessern, Erstellung der DB Verbindung reinpacken | | 18
o | Quelle für Overhead suchen | | 27
