glidingthroughspace/paper-tracker/meta/pictures/pico-battery01.jpg

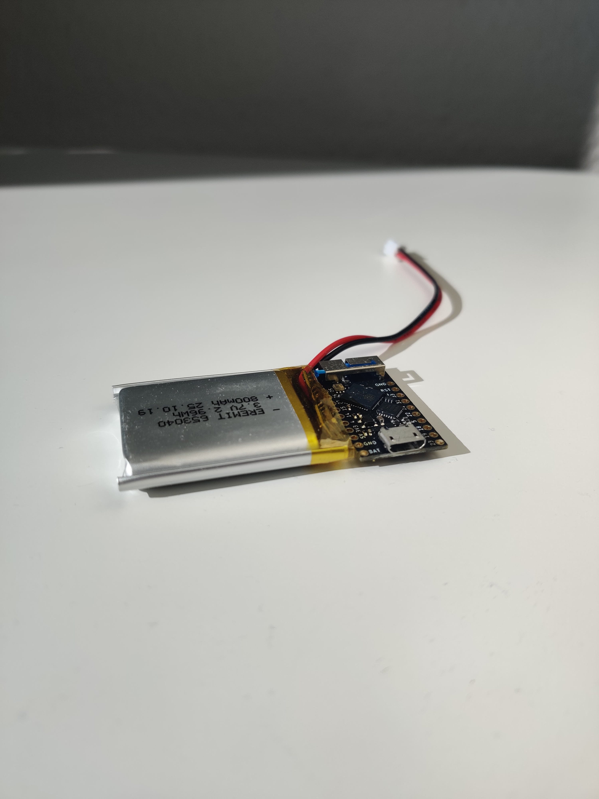
meta/pictures/pico-battery01.jpg
