glidingthroughspace/paper-tracker/meta/pictures/pico-battery02.jpg

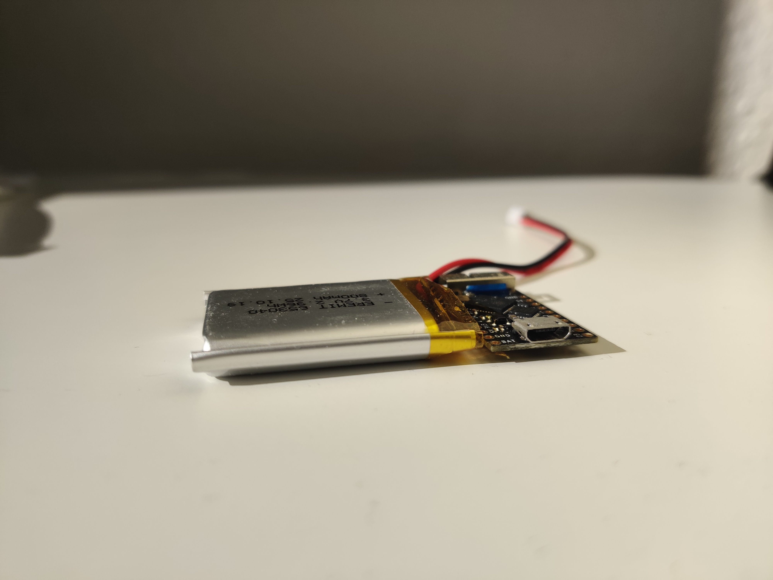
meta/pictures/pico-battery02.jpg
