glidingthroughspace/paper-tracker/meta/pictures/pico-battery05.jpg

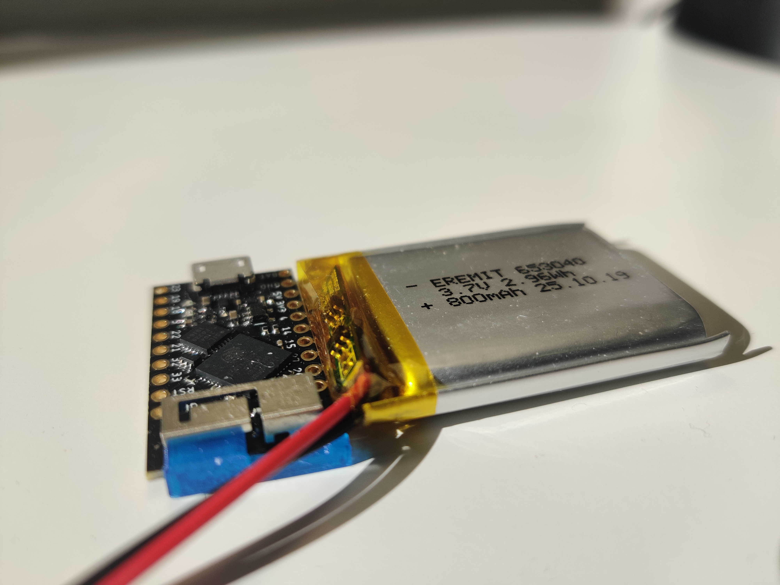
meta/pictures/pico-battery05.jpg
