glidingthroughspace/paper-tracker/meta/pictures/pico-battery07.jpg

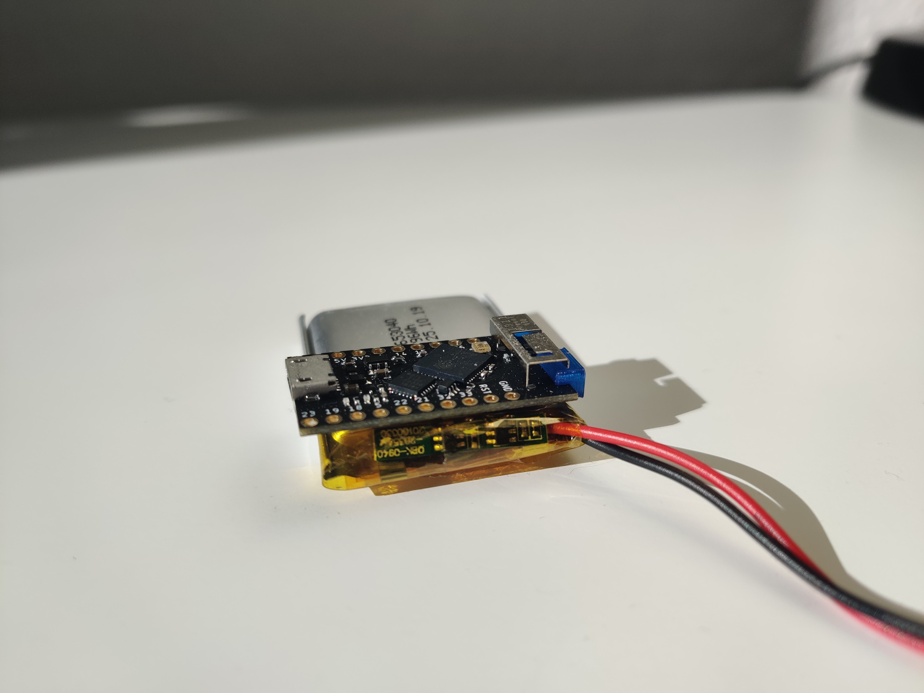
meta/pictures/pico-battery07.jpg
