glidingthroughspace/paper-tracker/meta/pictures/pico-battery08.jpg

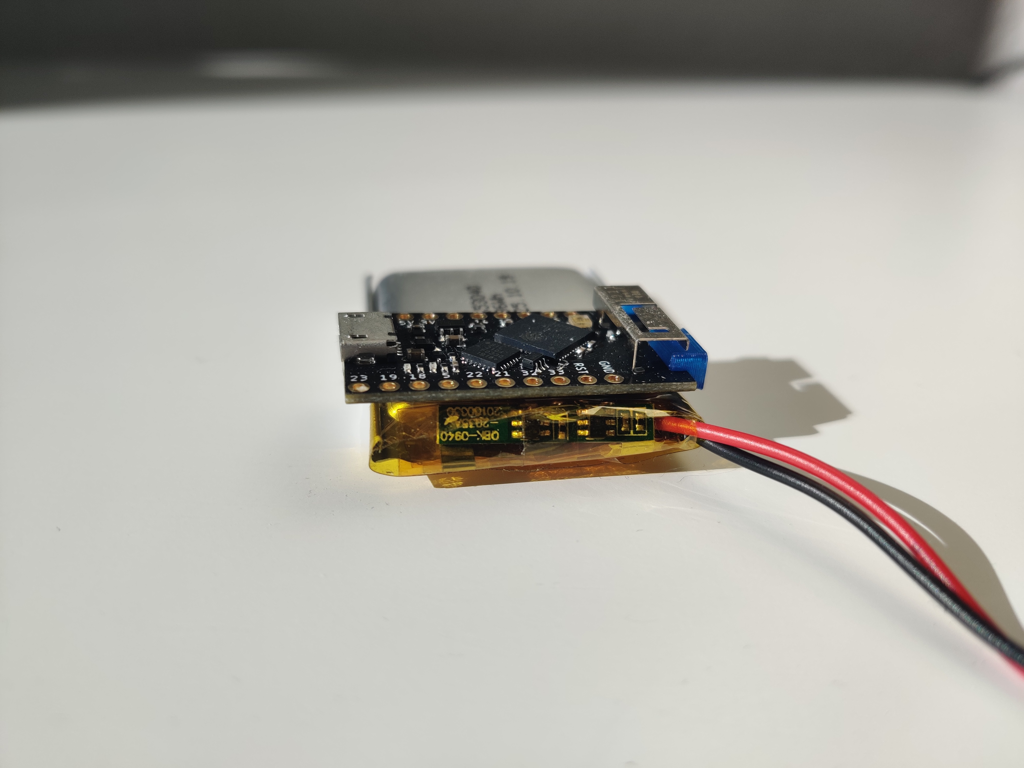
meta/pictures/pico-battery08.jpg
