glidingthroughspace/paper-tracker/meta/pictures/pico-battery09.jpg

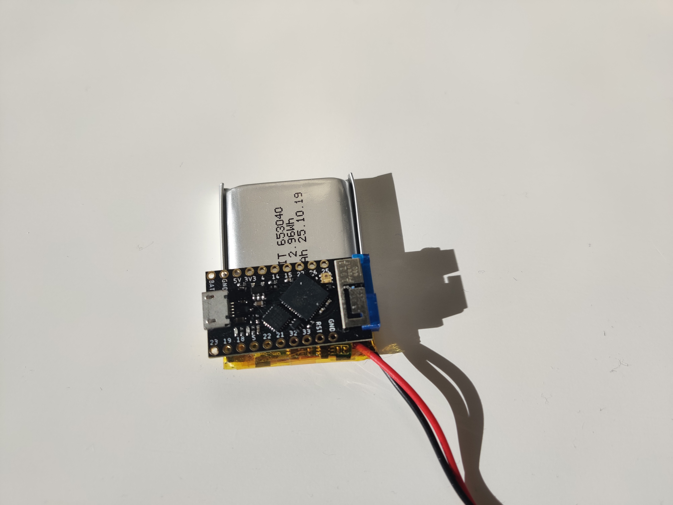
meta/pictures/pico-battery09.jpg
