glidingthroughspace/paper-tracker/meta/pictures/pico-battery10.jpg

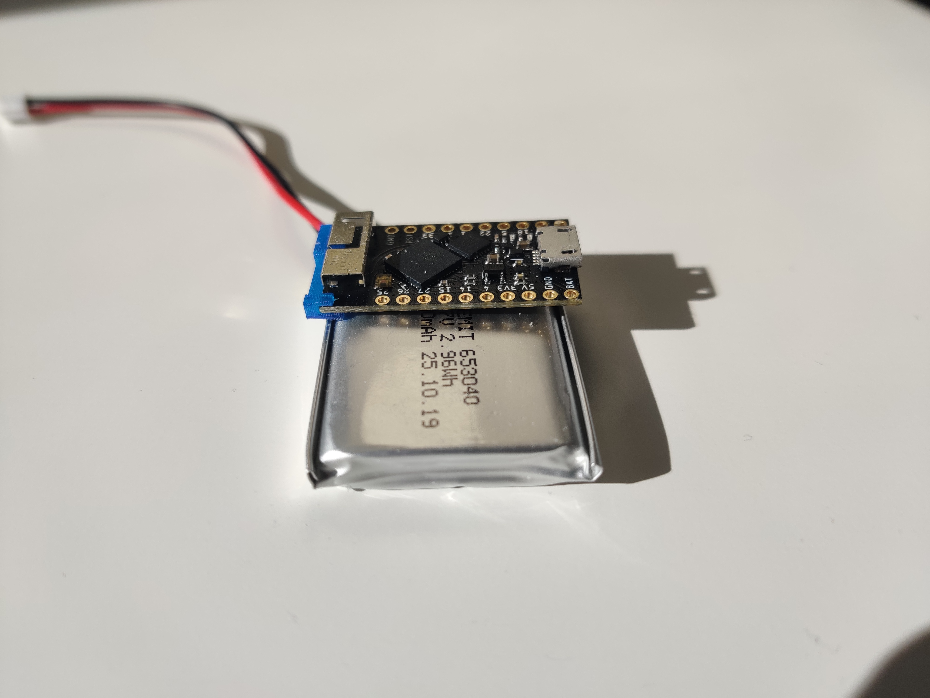
meta/pictures/pico-battery10.jpg
