glidingthroughspace/paper-tracker/paper/images/battery-runtime-slowtrack.png

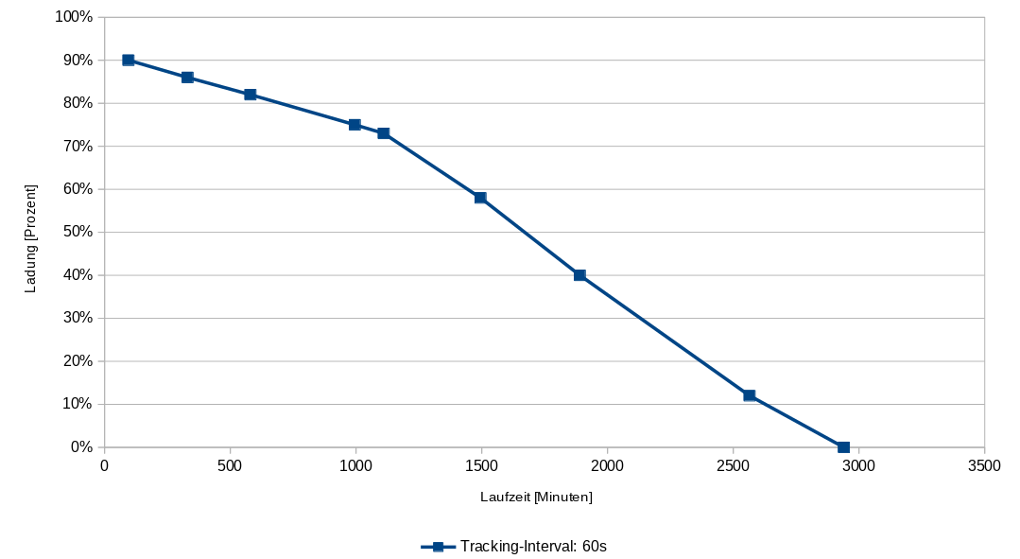
paper/images/battery-runtime-slowtrack.png
