glidingthroughspace/paper-tracker/app/assets/images/tutorial_0.png

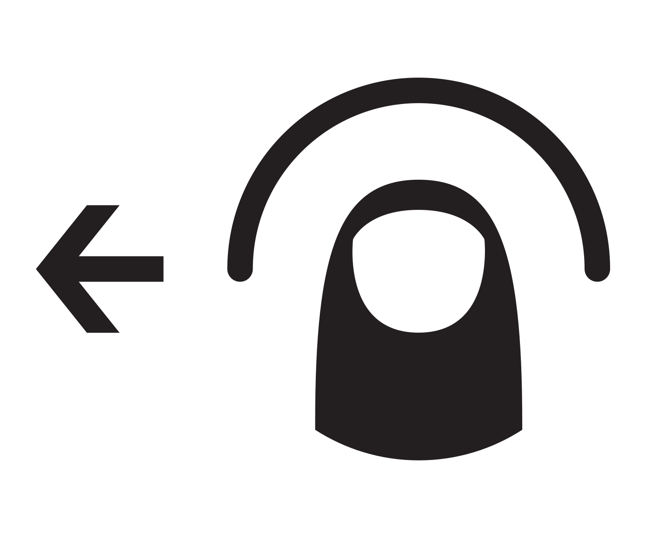
app/assets/images/tutorial_0.png
