glidingthroughspace/paper-tracker/app/assets/images/tutorial_2.png

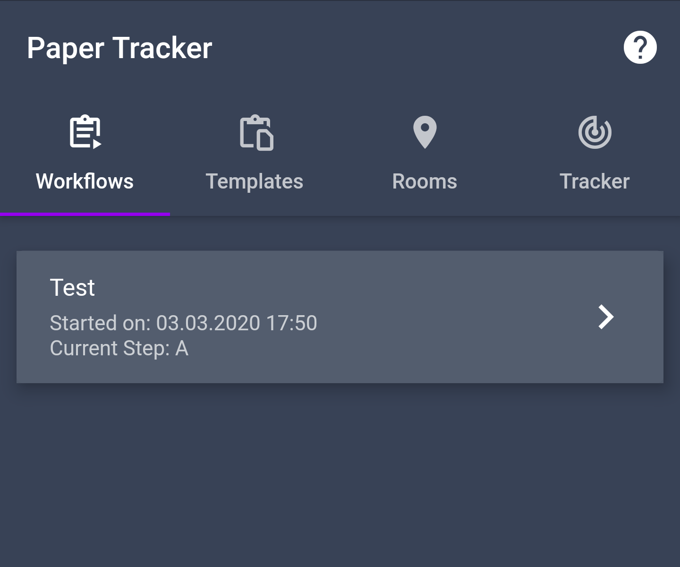
app/assets/images/tutorial_2.png
