glidingthroughspace/paper-tracker/app/assets/images/tutorial_3.png

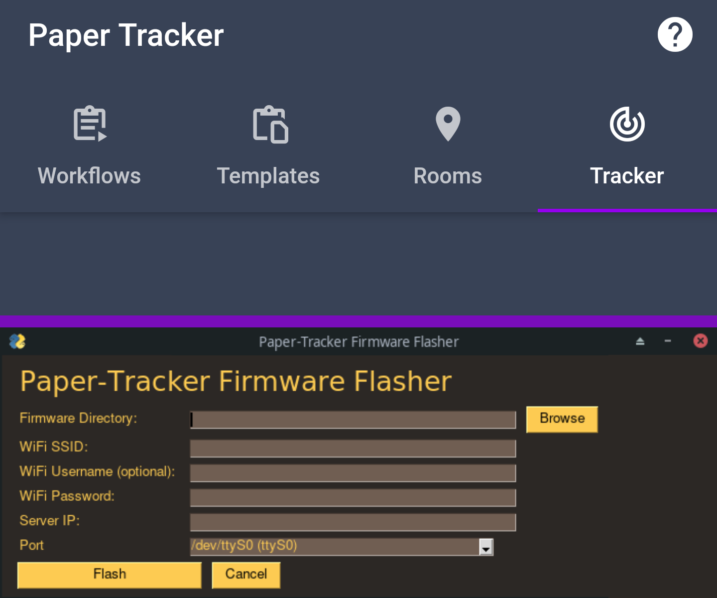
app/assets/images/tutorial_3.png
