glidingthroughspace/paper-tracker/app/assets/images/tutorial_4.png

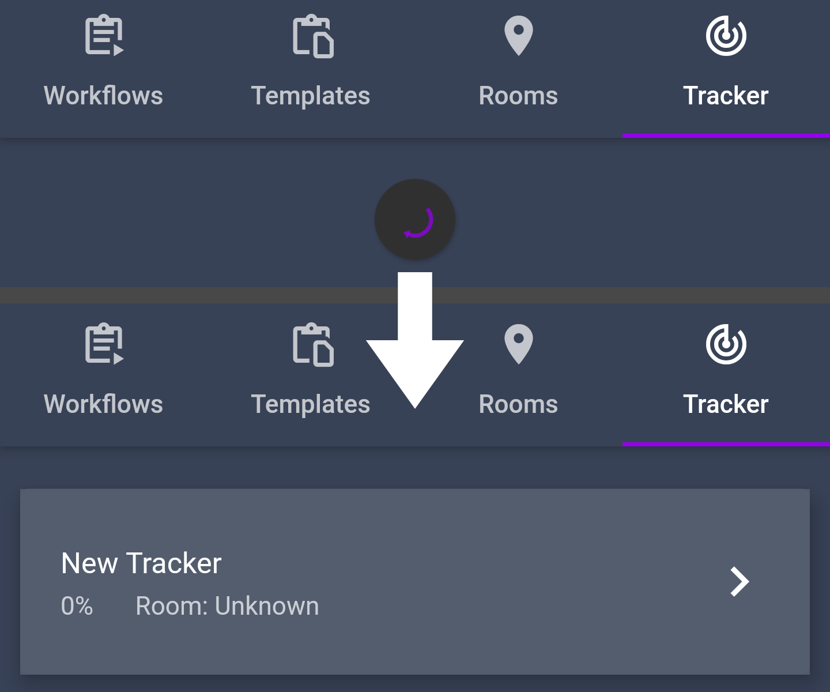
app/assets/images/tutorial_4.png
