glidingthroughspace/paper-tracker/app/assets/images/tutorial_5.png

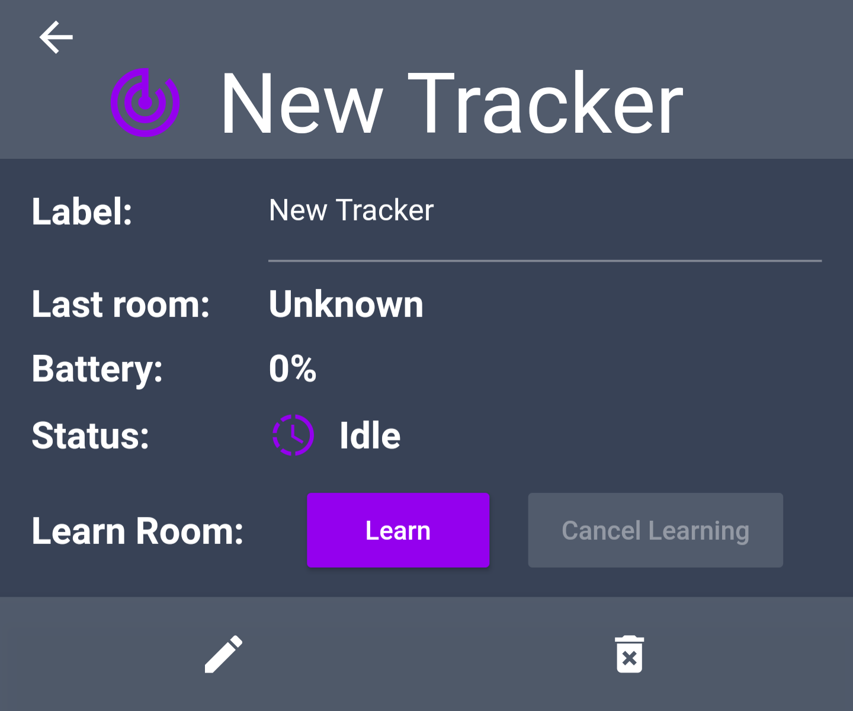
app/assets/images/tutorial_5.png
