glidingthroughspace/paper-tracker/app/assets/images/tutorial_7.png

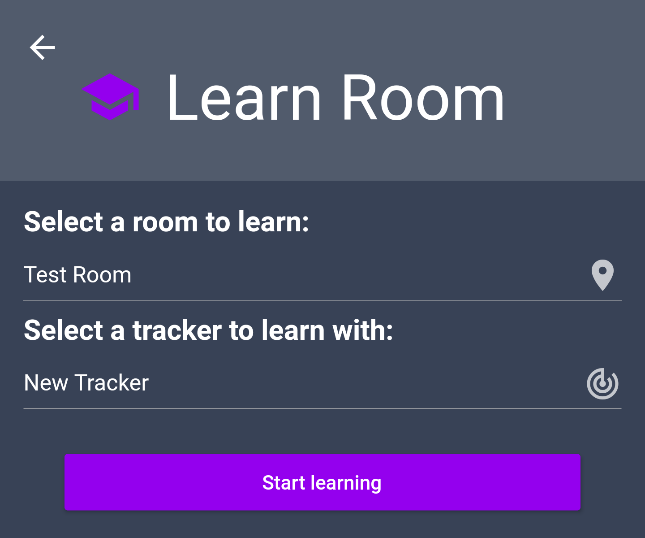
app/assets/images/tutorial_7.png
