glidingthroughspace/paper-tracker/app/assets/images/tutorial_8.png

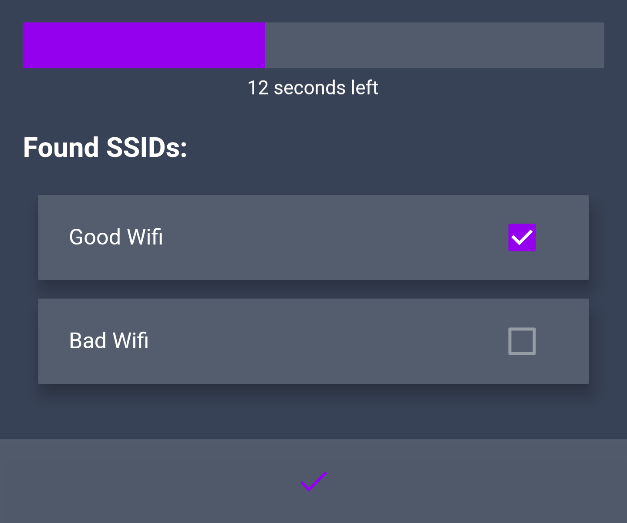
app/assets/images/tutorial_8.png
