glidingthroughspace/paper-tracker/app/assets/images/tutorial_10.png

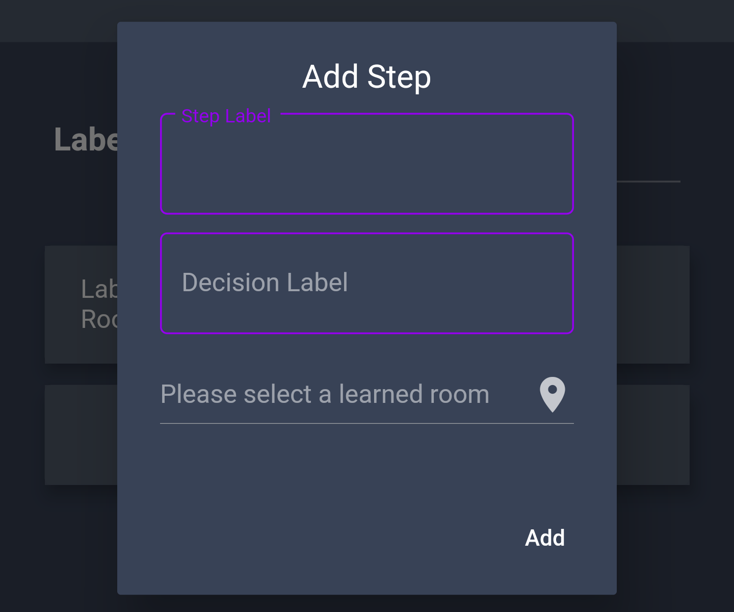
app/assets/images/tutorial_10.png
