glidingthroughspace/paper-tracker/app/assets/images/tutorial_12.png

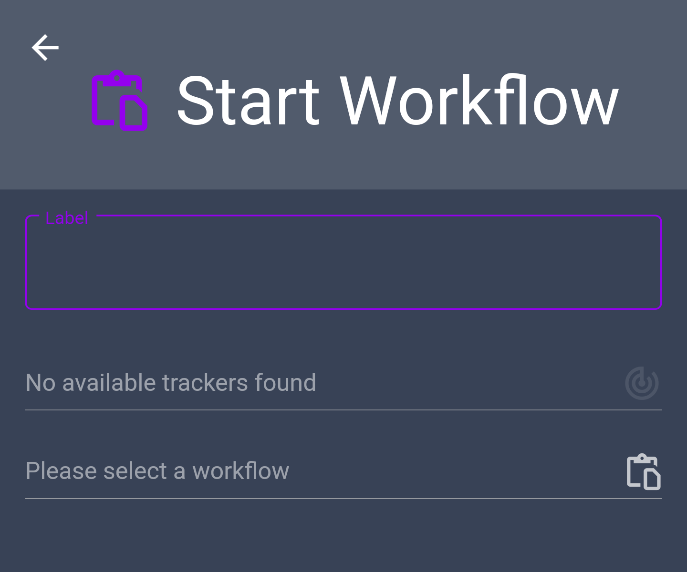
app/assets/images/tutorial_12.png
